teddycool/BinaryClock/21-20-42.jpg

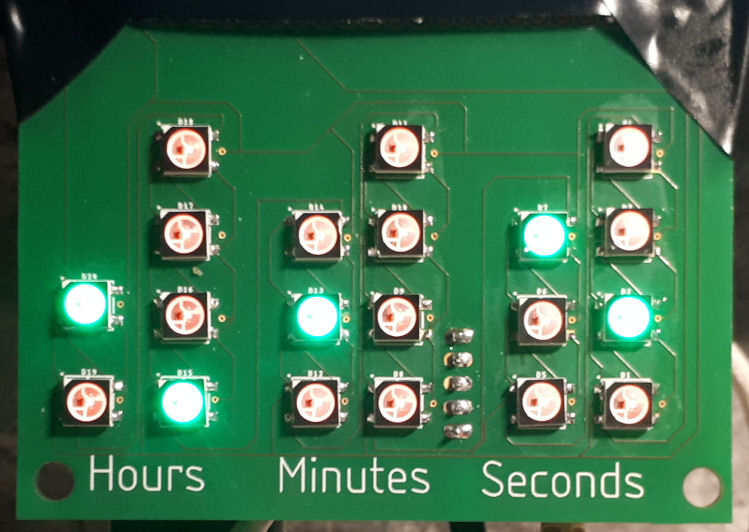
21-20-42.jpg
