teddycool/BinaryClock/20190211_194020.jpg

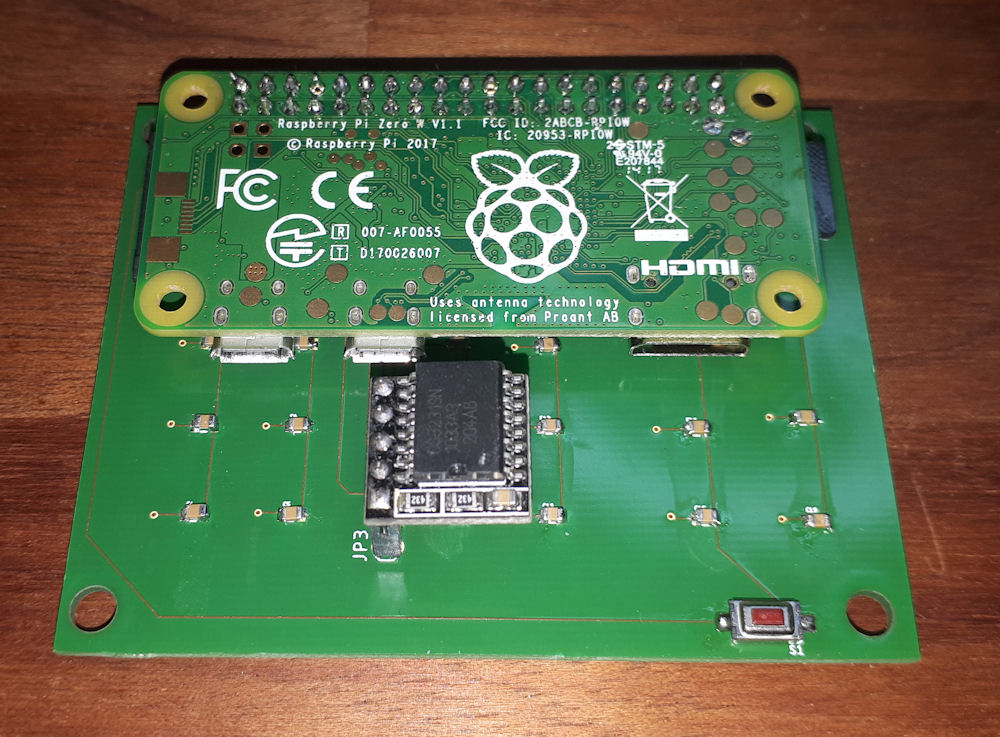
20190211_194020.jpg
