teddycool/BinaryClock/20190211_194517.jpg

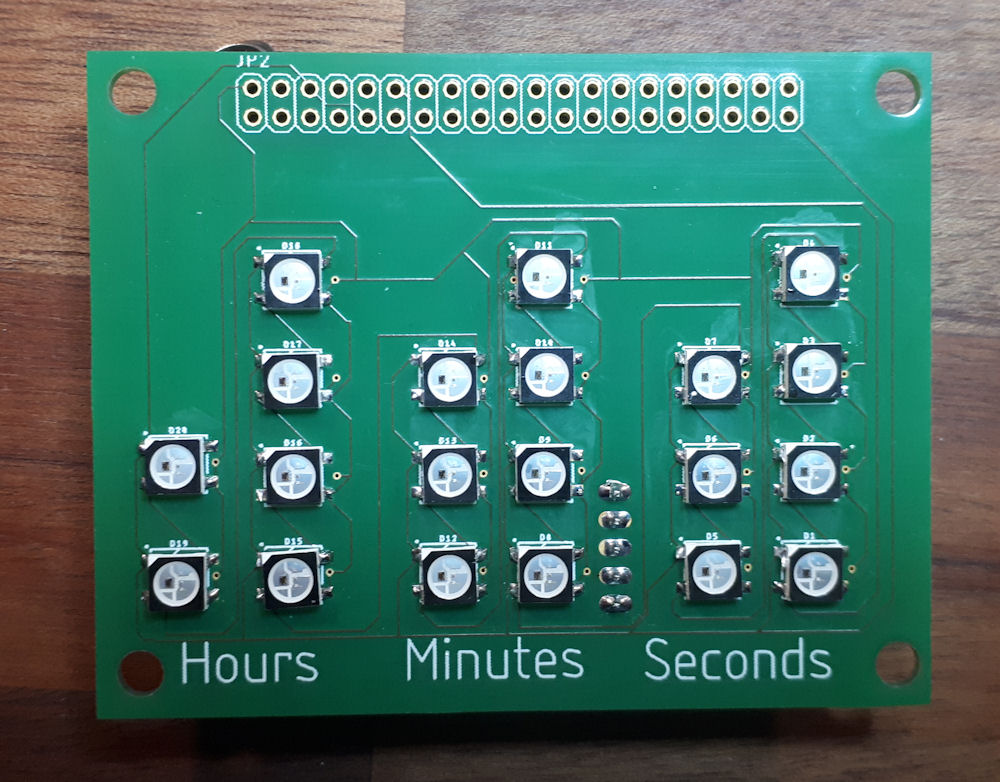
20190211_194517.jpg
