teddycool/BinaryClock/PyBinaryClock/Config.py

GeneralSettings = {"HW-version": 1, "DefaultBrightness": 50, "TempMax": 60, "SSID": "***", "PSK": "***"}

Networks= {"Name": {"ssid": "", "psk": ""}, }

Timers = {}

Wpa_Cli = {"FilePath": "", }

Logger = {"Level": "debug", "FilePath": ""}

LoggerApi = ""
